waveshareteam/ESP32-C5-Touch-LCD-2.8/example/Arduino-v3.3.10/example/02_I2C_qmi8658/i2c_bsp.cpp

#include <stdio.h>
#include "i2c_bsp.h"


#define TEST_I2C_PORT I2C_NUM_0
//#define EXAMPLE_USE_TOUCH   //Touch screen implementation


#ifndef EXAMPLE_USE_TOUCH

#define I2C_MASTER_SCL_IO 1
#define I2C_MASTER_SDA_IO 0

void I2C_master_Init(void)
{
  i2c_config_t conf = 
  {
    .mode = I2C_MODE_MASTER,
    .sda_io_num = I2C_MASTER_SDA_IO,         // Configure GPIO for SDA
    .scl_io_num = I2C_MASTER_SCL_IO,         // Configure GPIO for SCL
    .sda_pullup_en = GPIO_PULLUP_ENABLE,
    .scl_pullup_en = GPIO_PULLUP_ENABLE,
    .master = {
      .clk_speed = 400 * 1000,
    },  // Select a frequency for the project
    .clk_flags = 0,          // Optionally, use the I2C SCLK SRC FLAG * flag to select the I2C source clock
  };
  ESP_ERROR_CHECK(i2c_param_config(TEST_I2C_PORT, &conf));
  ESP_ERROR_CHECK(i2c_driver_install(TEST_I2C_PORT, conf.mode,0,0,0));
}
#endif

uint8_t I2C_writr_buff(uint8_t addr,uint8_t reg,uint8_t *buf,uint8_t len)
{
  uint8_t ret;
  uint8_t *pbuf = (uint8_t*)malloc(len+1);
  pbuf[0] = reg;
  for(uint8_t i = 0; i<len; i++)
  {
    pbuf[i+1] = buf[i];
  }
  ret = i2c_master_write_to_device(TEST_I2C_PORT,addr,pbuf,len+1,1000);
  free(pbuf);
  pbuf = NULL;
  return ret;
}
uint8_t I2C_read_buff(uint8_t addr,uint8_t reg,uint8_t *buf,uint8_t len)
{
  uint8_t ret;
  ret = i2c_master_write_read_device(TEST_I2C_PORT,addr,&reg,1,buf,len,1000);
  return ret;
}
uint8_t I2C_master_write_read_device(uint8_t addr,uint8_t *writeBuf,uint8_t writeLen,uint8_t *readBuf,uint8_t readLen)
{
  uint8_t ret;
  ret = i2c_master_write_read_device(TEST_I2C_PORT,addr,writeBuf,writeLen,readBuf,readLen,1000);
  return ret;
}
